Talgat047/offzone-addon-s7/project/offzone-addon-s7.kicad_sch

## KiCad design project/offzone-addon-s7.kicad_sch (2026-08-14)

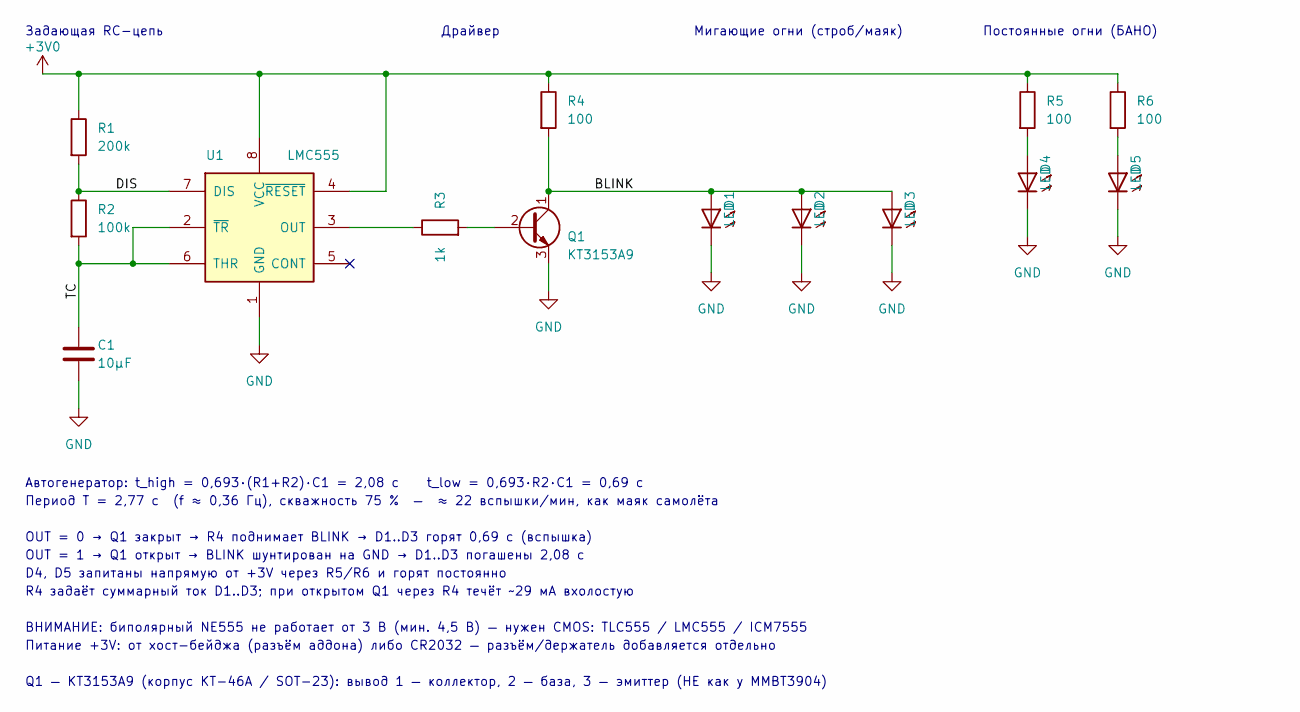
[picture p2: schematic offzone-addon-s7.kicad_sch]

Parts:
C1: 10µF
D1, D2, D3, D4, D5: LED
Q1: KT3153A9
R1: 200k
R2: 100k
R3: 1k
R4, R5, R6: 100
U1: LMC555

Connections:
+3V0: R1.1, R4.1, R5.1, R6.1, U1.4 (~RESET), U1.8 (VCC)
BLINK: D1.2 (A), D2.2 (A), D3.2 (A), Q1.1 (C), R4.2
DIS: R1.2, R2.1, U1.7 (DIS)
GND: C1.2, D1.1 (K), D2.1 (K), D3.1 (K), D4.1 (K), D5.1 (K), Q1.3 (E), U1.1 (GND)
unnamed: D4.2 (A), R5.2
unnamed: D5.2 (A), R6.2
unnamed: Q1.2 (B), R3.2
unnamed: R3.1, U1.3 (OUT)
TC: C1.1, R2.2, U1.2 (~TR), U1.6 (THR)

Notes on the sheet:
Задающая RC-цепь
Драйвер
Мигающие огни (строб/маяк)
Постоянные огни (БАНО)
Автогенератор: t_high = 0,693·(R1+R2)·C1 = 2,08 c t_low = 0,693·R2·C1 = 0,69 c
Период T = 2,77 c (f ≈ 0,36 Гц), скважность 75 % — ≈ 22 вспышки/мин, как маяк самолёта
OUT = 0 → Q1 закрыт → R4 поднимает BLINK → D1..D3 горят 0,69 c (вспышка)
OUT = 1 → Q1 открыт → BLINK шунтирован на GND → D1..D3 погашены 2,08 c
D4, D5 запитаны напрямую от +3V через R5/R6 и горят постоянно
R4 задаёт суммарный ток D1..D3; при открытом Q1 через R4 течёт ~29 мА вхолостую
ВНИМАНИЕ: биполярный NE555 не работает от 3 В (мин. 4,5 В) — нужен CMOS: TLC555 / LMC555 / ICM7555
Питание +3V: от хост-бейджа (разъём аддона) либо CR2032 — разъём/держатель добавляется отдельно
Q1 — КТ3153А9 (корпус КТ-46А / SOT-23): вывод 1 — коллектор, 2 — база, 3 — эмиттер (НЕ как у MMBT3904)
